vic42/usb_moodlight/kicad/mood_light.sch

## KiCad design kicad/mood_light.sch (2013-01-24)

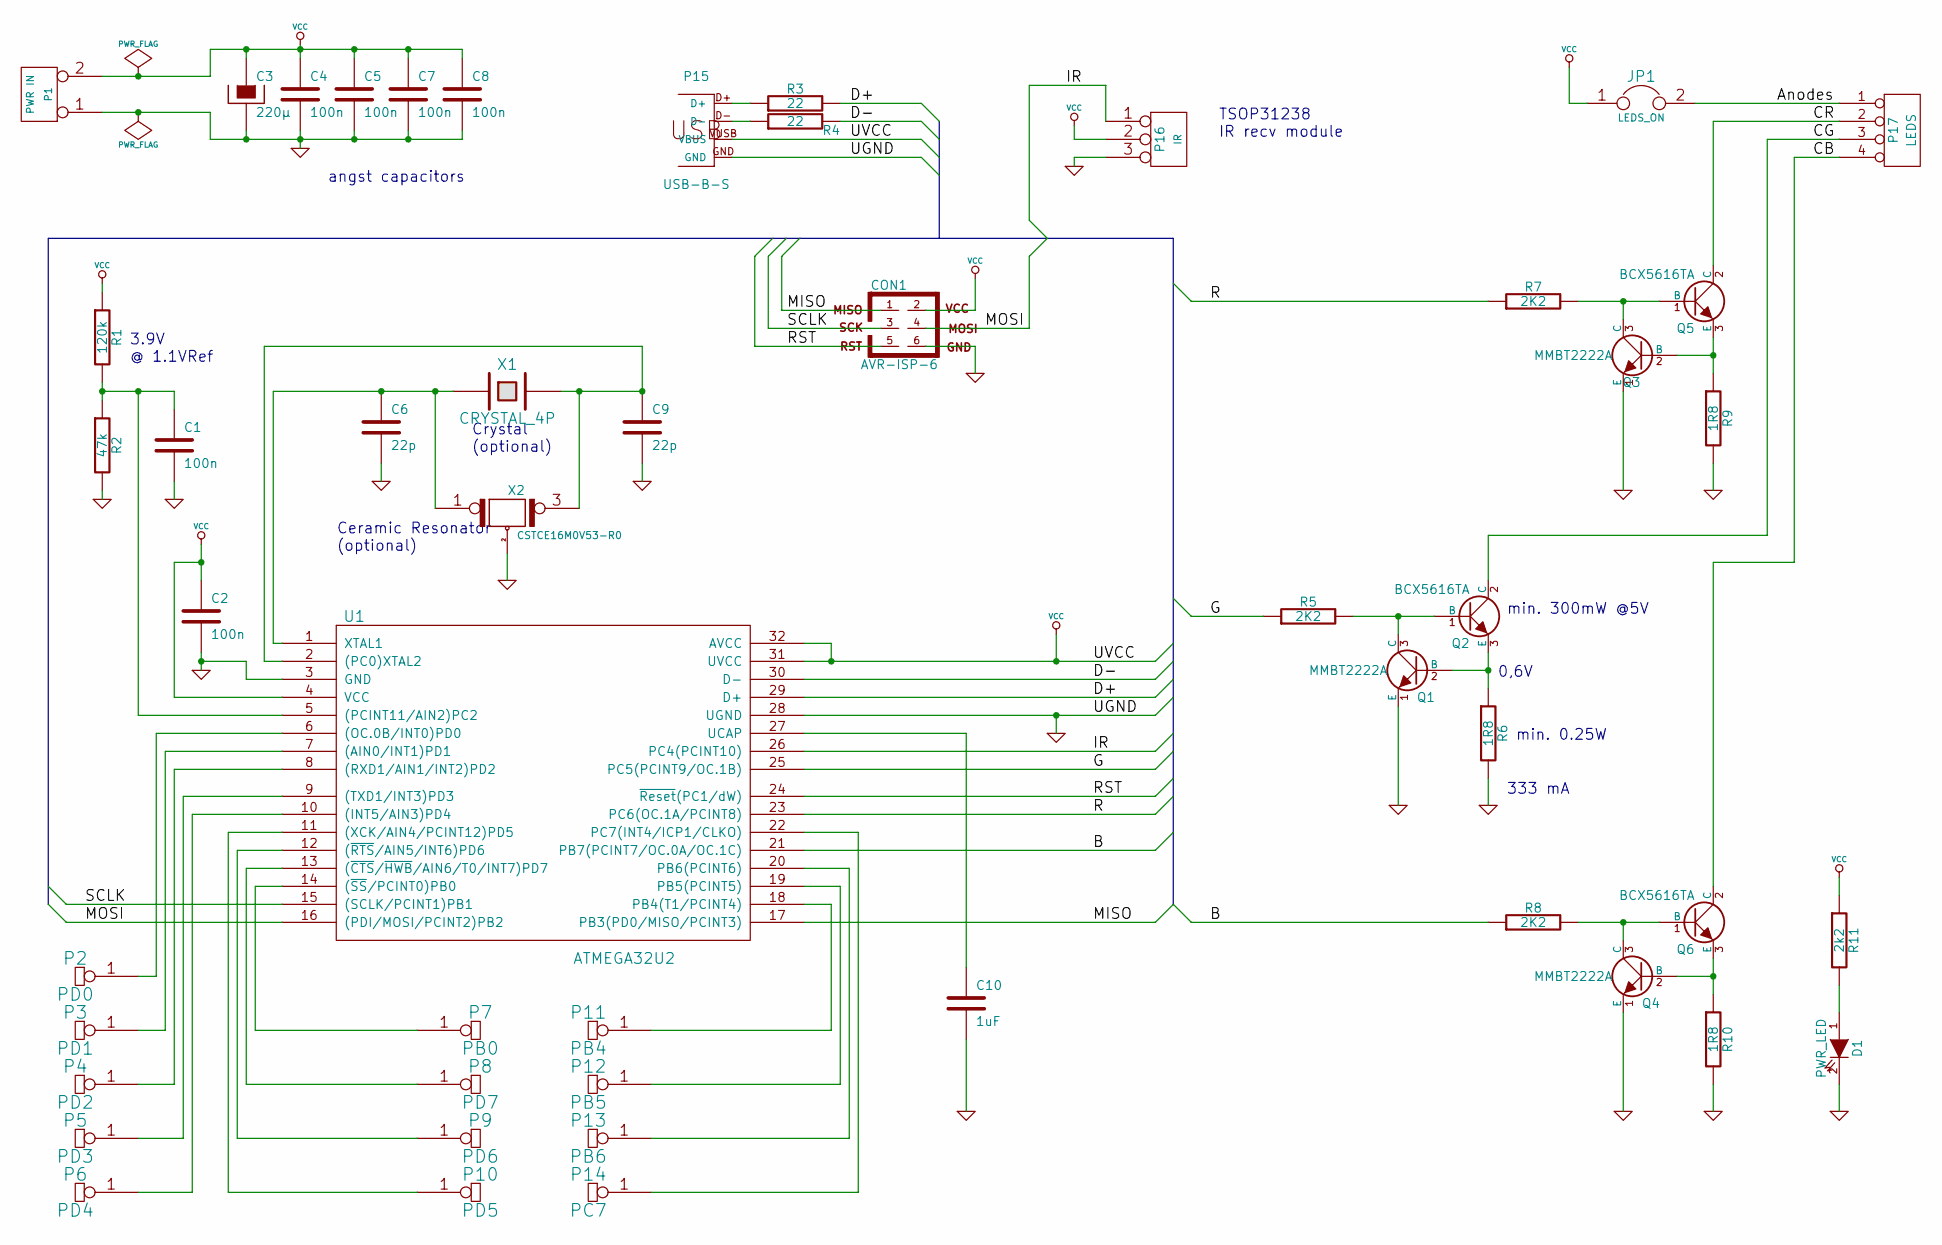
[picture p4: schematic mood_light.sch]

Parts:
C1, C2, C4, C5, C7, C8: 100n
C3: 220µ
C6, C9: 22p
C10: 1uF
CON1: AVR-ISP-6
D1: PWR_LED
JP1: LEDS_ON
P1: PWR IN
P2: PD0
P3: PD1
P4: PD2
P5: PD3
P6: PD4
P7: PB0
P8: PD7
P9: PD6
P10: PD5
P11: PB4
P12: PB5
P13: PB6
P14: PC7
P15: USB-B-S; con-usb-USB-B-SMT
P16: IR
P17: LEDS
Q1, Q3, Q4: MMBT2222A
Q2, Q5, Q6: BCX5616TA
R1: 120k
R2: 47k
R3, R4: 22
R5, R7, R8: 2K2
R6, R9, R10: 1R8
R11: 2k2
U1: ATMEGA32U2; TQFP32
X1: CRYSTAL_4P
X2: CSTCE16M0V53-R0

Connections:
Anodes: JP1.2, P17.1
B: R8.1, U1.21 (PB7(PCINT7/OC.0A/OC.1C))
CB: P17.4, Q6.2 (C)
CG: P17.3, Q2.2 (C)
CR: P17.2, Q5.2 (C)
D+: R3.2, U1.29 (D+)
D-: R4.2, U1.30 (D-)
G: R5.1, U1.25 (PC5(PCINT9/OC.1B))
GND: C1.2, C2.2, C3.2, C4.2, C5.2, C6.2, C7.2, C8.2, C9.2, C10.2, CON1.6, D1.2 (K), P1.1, P15.GND, P16.3, Q1.1 (E), Q3.1 (E), Q4.1 (E), R2.2, R6.2, R9.2, R10.2, U1.3 (GND), U1.28 (UGND), X2.2 (PM)
IR: P16.1, U1.26 (PC4(PCINT10))
MISO: CON1.1, U1.17 (PB3(PD0/MISO/PCINT3))
MOSI: CON1.4, U1.16 ((PDI/MOSI/PCINT2)PB2)
unnamed: C1.1, R1.2, R2.1, U1.5 ((PCINT11/AIN2)PC2)
unnamed: C6.1, U1.1 (XTAL1), X1.1 (X), X2.1
unnamed: C9.1, U1.2 ((PC0)XTAL2), X1.2 (X), X2.3
unnamed: C10.1, U1.27 (UCAP)
unnamed: D1.1 (A), R11.2
unnamed: P2.1, U1.6 ((OC.0B/INT0)PD0)
unnamed: P3.1, U1.7 ((AIN0/INT1)PD1)
unnamed: P4.1, U1.8 ((RXD1/AIN1/INT2)PD2)
unnamed: P5.1, U1.9 ((TXD1/INT3)PD3)
unnamed: P6.1, U1.10 ((INT5/AIN3)PD4)
unnamed: P7.1, U1.14 ((~SS~/PCINT0)PB0)
unnamed: P8.1, U1.13 ((~CTS~/~HWB~/AIN6/T0/INT7)PD7)
unnamed: P9.1, U1.12 ((~RTS~/AIN5/INT6)PD6)
unnamed: P10.1, U1.11 ((XCK/AIN4/PCINT12)PD5)
unnamed: P11.1, U1.18 (PB4(T1/PCINT4))
unnamed: P12.1, U1.19 (PB5(PCINT5))
unnamed: P13.1, U1.20 (PB6(PCINT6))
unnamed: P14.1, U1.22 (PC7(INT4/ICP1/CLKO))
unnamed: P15.D+, R3.1
unnamed: P15.D-, R4.1
unnamed: Q1.2 (B), Q2.3 (E), R6.1
unnamed: Q1.3 (C), Q2.1 (B), R5.2
unnamed: Q3.2 (B), Q5.3 (E), R9.1
unnamed: Q3.3 (C), Q5.1 (B), R7.2
unnamed: Q4.2 (B), Q6.3 (E), R10.1
unnamed: Q4.3 (C), Q6.1 (B), R8.2
R: R7.1, U1.23 (PC6(OC.1A/PCINT8))
RST: CON1.5, U1.24 (~Reset~(PC1/dW))
SCLK: CON1.3, U1.15 ((SCLK/PCINT1)PB1)
VCC: C2.1, C3.1, C4.1, C5.1, C7.1, C8.1, CON1.2, JP1.1, P1.2 (PM), P15.VUSB (VBUS), P16.2 (PM), R1.1, R11.1, U1.4 (VCC), U1.31 (UVCC), U1.32 (AVCC)

Notes on the sheet:
Crystal (optional)
Ceramic Resonator (optional)
3.9V @ 1.1VRef
TSOP31238 IR recv module
angst capacitors
0,6V
min. 300mW @5V
333 mA
min. 0.25W
